derekfountain/zx-spectrum-diagnostics/pcb_pga2040/PGA2040_docs/pga2040_1024x1024.webp

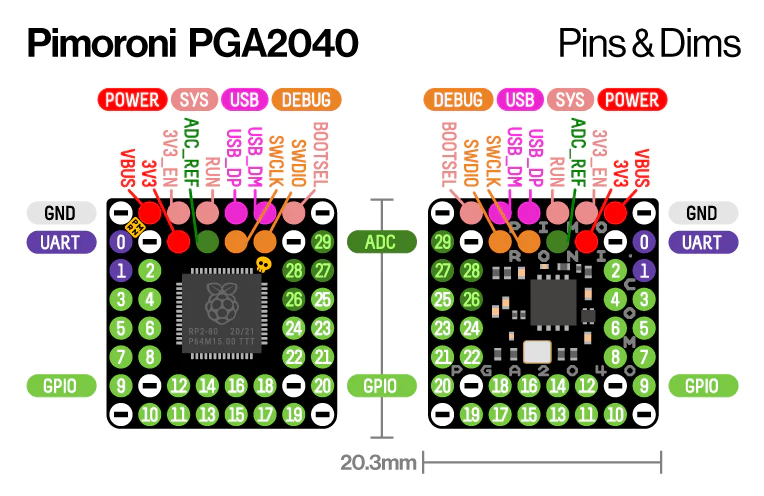
pcb_pga2040/PGA2040_docs/pga2040_1024x1024.webp
