derekfountain/zx-spectrum-diagnostics/pcb_pga2040/PGA2040_docs/pga-2040-on-white-2_1500x1500_crop_center.webp

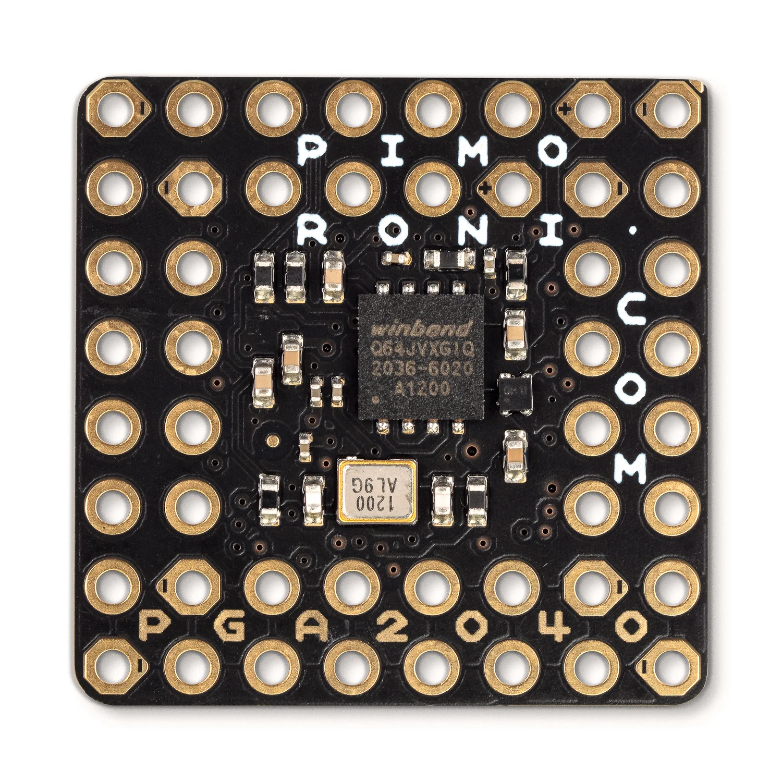
pcb_pga2040/PGA2040_docs/pga-2040-on-white-2_1500x1500_crop_center.webp
