derekfountain/zx-spectrum-diagnostics/firmware/pico1/page_dbus.c

/*
 * Data bus tests
 */

#include "oled.h"
#include "page.h"
#include "gpios.h"
#include "test_data.h"

#include "pico/stdlib.h"
#include <stdio.h>
#include <string.h>

/* Long enough to let the Spectrum boot and run a decent part of the ROM */
#define TEST_TIME_SECS   2
#define TEST_TIME_SECS_F ((float)(TEST_TIME_SECS))

#define NUM_DBUS_TEST_RESULT_LINES 3
#define WIDTH_OLED_CHARS 32
static uint8_t result_line_txt[NUM_DBUS_TEST_RESULT_LINES][WIDTH_OLED_CHARS+1];

#define NUM_DBUS_LINES 8

static EDGE_STATUS bus_status[NUM_DBUS_LINES ] =
{
  {SEEN_NEITHER, GPIO_DBUS_D0},
  {SEEN_NEITHER, GPIO_DBUS_D1},
  {SEEN_NEITHER, GPIO_DBUS_D2},
  {SEEN_NEITHER, GPIO_DBUS_D3},
  {SEEN_NEITHER, GPIO_DBUS_D4},
  {SEEN_NEITHER, GPIO_DBUS_D5},
  {SEEN_NEITHER, GPIO_DBUS_D6},
  {SEEN_NEITHER, GPIO_DBUS_D7},
};

static bool dbus_test_running = false;

static int64_t __time_critical_func(dbus_alarm_callback)(alarm_id_t id, void *user_data)
{
  dbus_test_running = false;
  return 0;
}

void dbus_page_init( void )
{
  /* Set up the data bus sampling GPIOs */
  for( uint32_t bus_index=0; bus_index<NUM_DBUS_LINES; bus_index++ )
  {
    gpio_init( bus_status[bus_index].gpio );
    gpio_set_dir( bus_status[bus_index].gpio, GPIO_IN );
    gpio_pull_up( bus_status[bus_index].gpio );
  }
}

void dbus_page_entry( void )
{
  /* Need to hold the Z80 offline while I set these up or they fire too early */
  gpio_put( GPIO_Z80_RESET, 1 ); sleep_ms( 650 );

  for( uint32_t bus_index=0; bus_index<NUM_DBUS_LINES; bus_index++ )
  {
    gpio_set_irq_enabled( bus_status[bus_index].gpio, GPIO_IRQ_EDGE_FALL|GPIO_IRQ_EDGE_RISE, true );
  }
}

void dbus_page_exit( void )
{
  for( uint32_t bus_index=0; bus_index<NUM_DBUS_LINES; bus_index++ )
  {
    gpio_set_irq_enabled( bus_status[bus_index].gpio, GPIO_IRQ_EDGE_FALL|GPIO_IRQ_EDGE_RISE, false );
  }

  snprintf( result_line_txt[0], WIDTH_OLED_CHARS, "        76543210" );
  snprintf( result_line_txt[1], WIDTH_OLED_CHARS, "        --------" );
  if( (bus_status[0].flag == SEEN_BOTH) &&
      (bus_status[1].flag == SEEN_BOTH) &&
      (bus_status[2].flag == SEEN_BOTH) &&
      (bus_status[3].flag == SEEN_BOTH) &&
      (bus_status[4].flag == SEEN_BOTH) &&
      (bus_status[5].flag == SEEN_BOTH) &&
      (bus_status[6].flag == SEEN_BOTH) &&
      (bus_status[7].flag == SEEN_BOTH) )
  {
    /* This would be the norm: transitions low to high and high to low have both been seen */
    snprintf( result_line_txt[2], WIDTH_OLED_CHARS, "Active: YYYYYYYY");
  }
  else
  {
    /*
     * Logic is as follows: if flag is SEEN_NEITHER then there has been no edge is
     * either direction. The line is stuck in whatever state it's currently in, high
     * or low. So just read the GPIO state - that's how it's stuck.
     *
     * If the flag indicates the line has been seen going high, but not seen going
     * low, then it must be stuck in its current state which is high.
     *
     * If the flag indicates the line has been seen going low, but not seen going
     * high, then it must be stuck in its current state which is low.
     *
     * Whichever it is, the current state of the GPIO tells me whether it's stuck
     * high or low.
     */
    snprintf( result_line_txt[2], WIDTH_OLED_CHARS, " Stuck: %c%c%c%c%c%c%c%c",
	      bus_status[7].flag == SEEN_BOTH ? '.' : gpio_get( bus_status[7].gpio ) ? 'H' : 'L',
	      bus_status[6].flag == SEEN_BOTH ? '.' : gpio_get( bus_status[6].gpio ) ? 'H' : 'L',
	      bus_status[5].flag == SEEN_BOTH ? '.' : gpio_get( bus_status[5].gpio ) ? 'H' : 'L',
	      bus_status[4].flag == SEEN_BOTH ? '.' : gpio_get( bus_status[4].gpio ) ? 'H' : 'L',
	      bus_status[3].flag == SEEN_BOTH ? '.' : gpio_get( bus_status[3].gpio ) ? 'H' : 'L',
	      bus_status[2].flag == SEEN_BOTH ? '.' : gpio_get( bus_status[2].gpio ) ? 'H' : 'L',
	      bus_status[1].flag == SEEN_BOTH ? '.' : gpio_get( bus_status[1].gpio ) ? 'H' : 'L',
	      bus_status[0].flag == SEEN_BOTH ? '.' : gpio_get( bus_status[0].gpio ) ? 'H' : 'L');
  }
}

void dbus_page_gpios( uint32_t gpio, uint32_t events )
{
  if( dbus_test_running )
  {
    if( (gpio >= GPIO_DBUS_D0) && (gpio <= GPIO_DBUS_D7) )
    {
      uint line_index = gpio - GPIO_DBUS_D0;
 
      /*
       * One of the data bus GPIOs has changed state. Note whether it was
       * rising or falling. If it's been seen doing both, it behaviour is
       * confirmed as correct and the GPIO callback is switched off.
       */

      if( events | GPIO_IRQ_EDGE_FALL )
      {
	bus_status[line_index].flag |= SEEN_FALLING;
      }
      if( events | GPIO_IRQ_EDGE_RISE )
      {
	bus_status[line_index].flag |= SEEN_RISING;
      }

      if( bus_status[line_index].flag == SEEN_BOTH )
      {
	gpio_set_irq_enabled( bus_status[line_index].gpio, GPIO_IRQ_EDGE_FALL|GPIO_IRQ_EDGE_RISE, false );
      }
    }
    else
    {
      panic("DBUS code received invalid GPIO %d", gpio);
    }
  }
}

void dbus_page_run_tests( void )
{
  dbus_test_running = false;

  /*
   * Reboot the Spectrum.
   */
  gpio_put( GPIO_Z80_RESET, 1 ); sleep_ms( 5 );
  gpio_put( GPIO_Z80_RESET, 0 );

  /*
   * I had a 
   *  sleep_ms( 650 );
   * in here, which isn't really necessary because I want to start monitoring
   * the data bus as soon as the Z80 is ready to run. I don't need to pause.
   * Thing is, that paused effectively stopped the Pico. I think it was
   * because with the 8 data bus GPIOs set up and firing the callback, when
   * the Z80 runs the flood of callbacks overwhelmes the Pico and it stalls
   * before the code below which sets up the alarm. The alarm never happens
   * and the test apparently runs forever.
   * Maybe, not sure, but taking that sleep out fixes it.
   */

  /* Start the alarm which defines the duration of the test */
  dbus_test_running = true;
  alarm_id_t dbus_alarm_id = add_alarm_in_ms( TEST_TIME_SECS*1000, dbus_alarm_callback, NULL, false );
  if( dbus_alarm_id < 0 )
    panic("No alarms available in DBUS test");

  while( dbus_test_running );

  /*
   * Alarm is done with, this reset isn't necessary but if I change the
   * timing system something else might need to go here
   */
  cancel_alarm( dbus_alarm_id );
}


void dbus_output(void)
{
  uint8_t line=2;
  for( uint32_t test_index=0; test_index<NUM_DBUS_TEST_RESULT_LINES; test_index++ )
  {      
    draw_str(0, line*8, "                         " );
    draw_str(0, line*8, result_line_txt[test_index] );      
	
    line++;
  }  
}
